ariq-dotcom/robotic-arm/Dokumentasi/2.jpeg

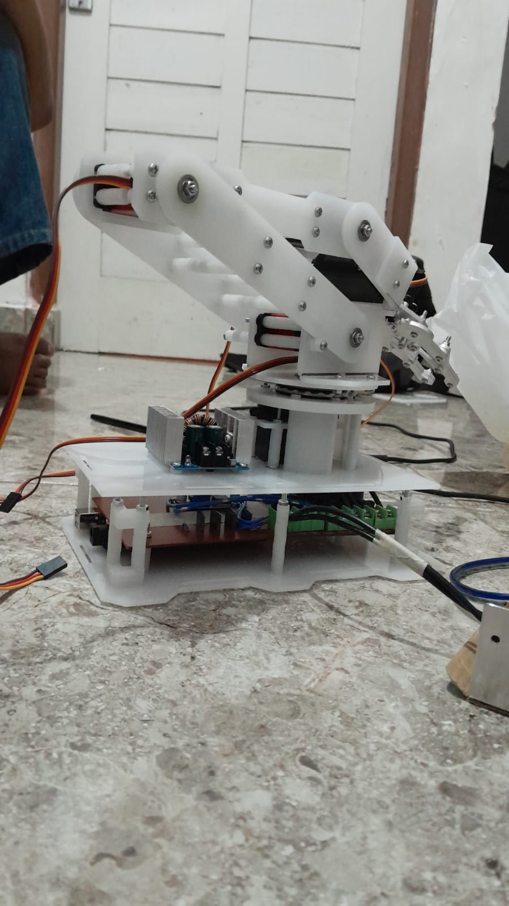
Dokumentasi/2.jpeg
