ariq-dotcom/robotic-arm/Dokumentasi/3.jpeg

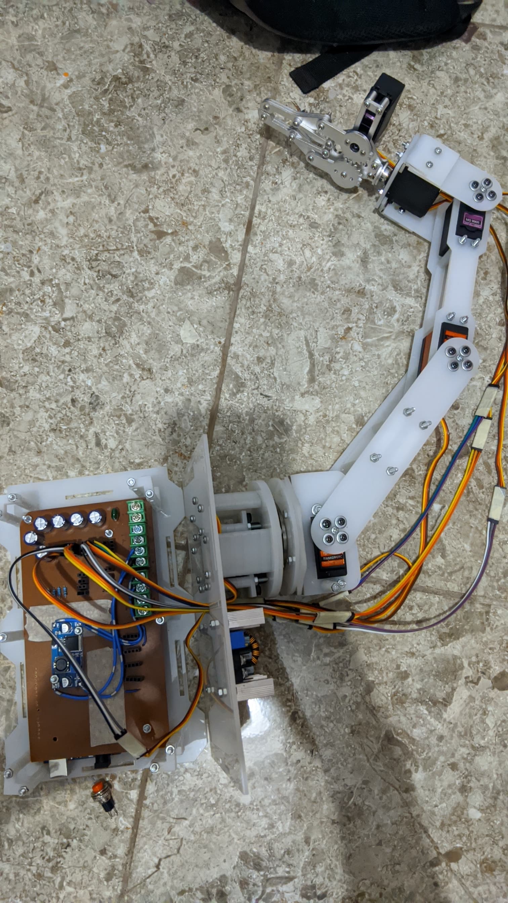
Dokumentasi/3.jpeg
